MarkMakies/Roverling/Roverling102.kicad_sch

## KiCad design Roverling102.kicad_sch (2023-07-21)

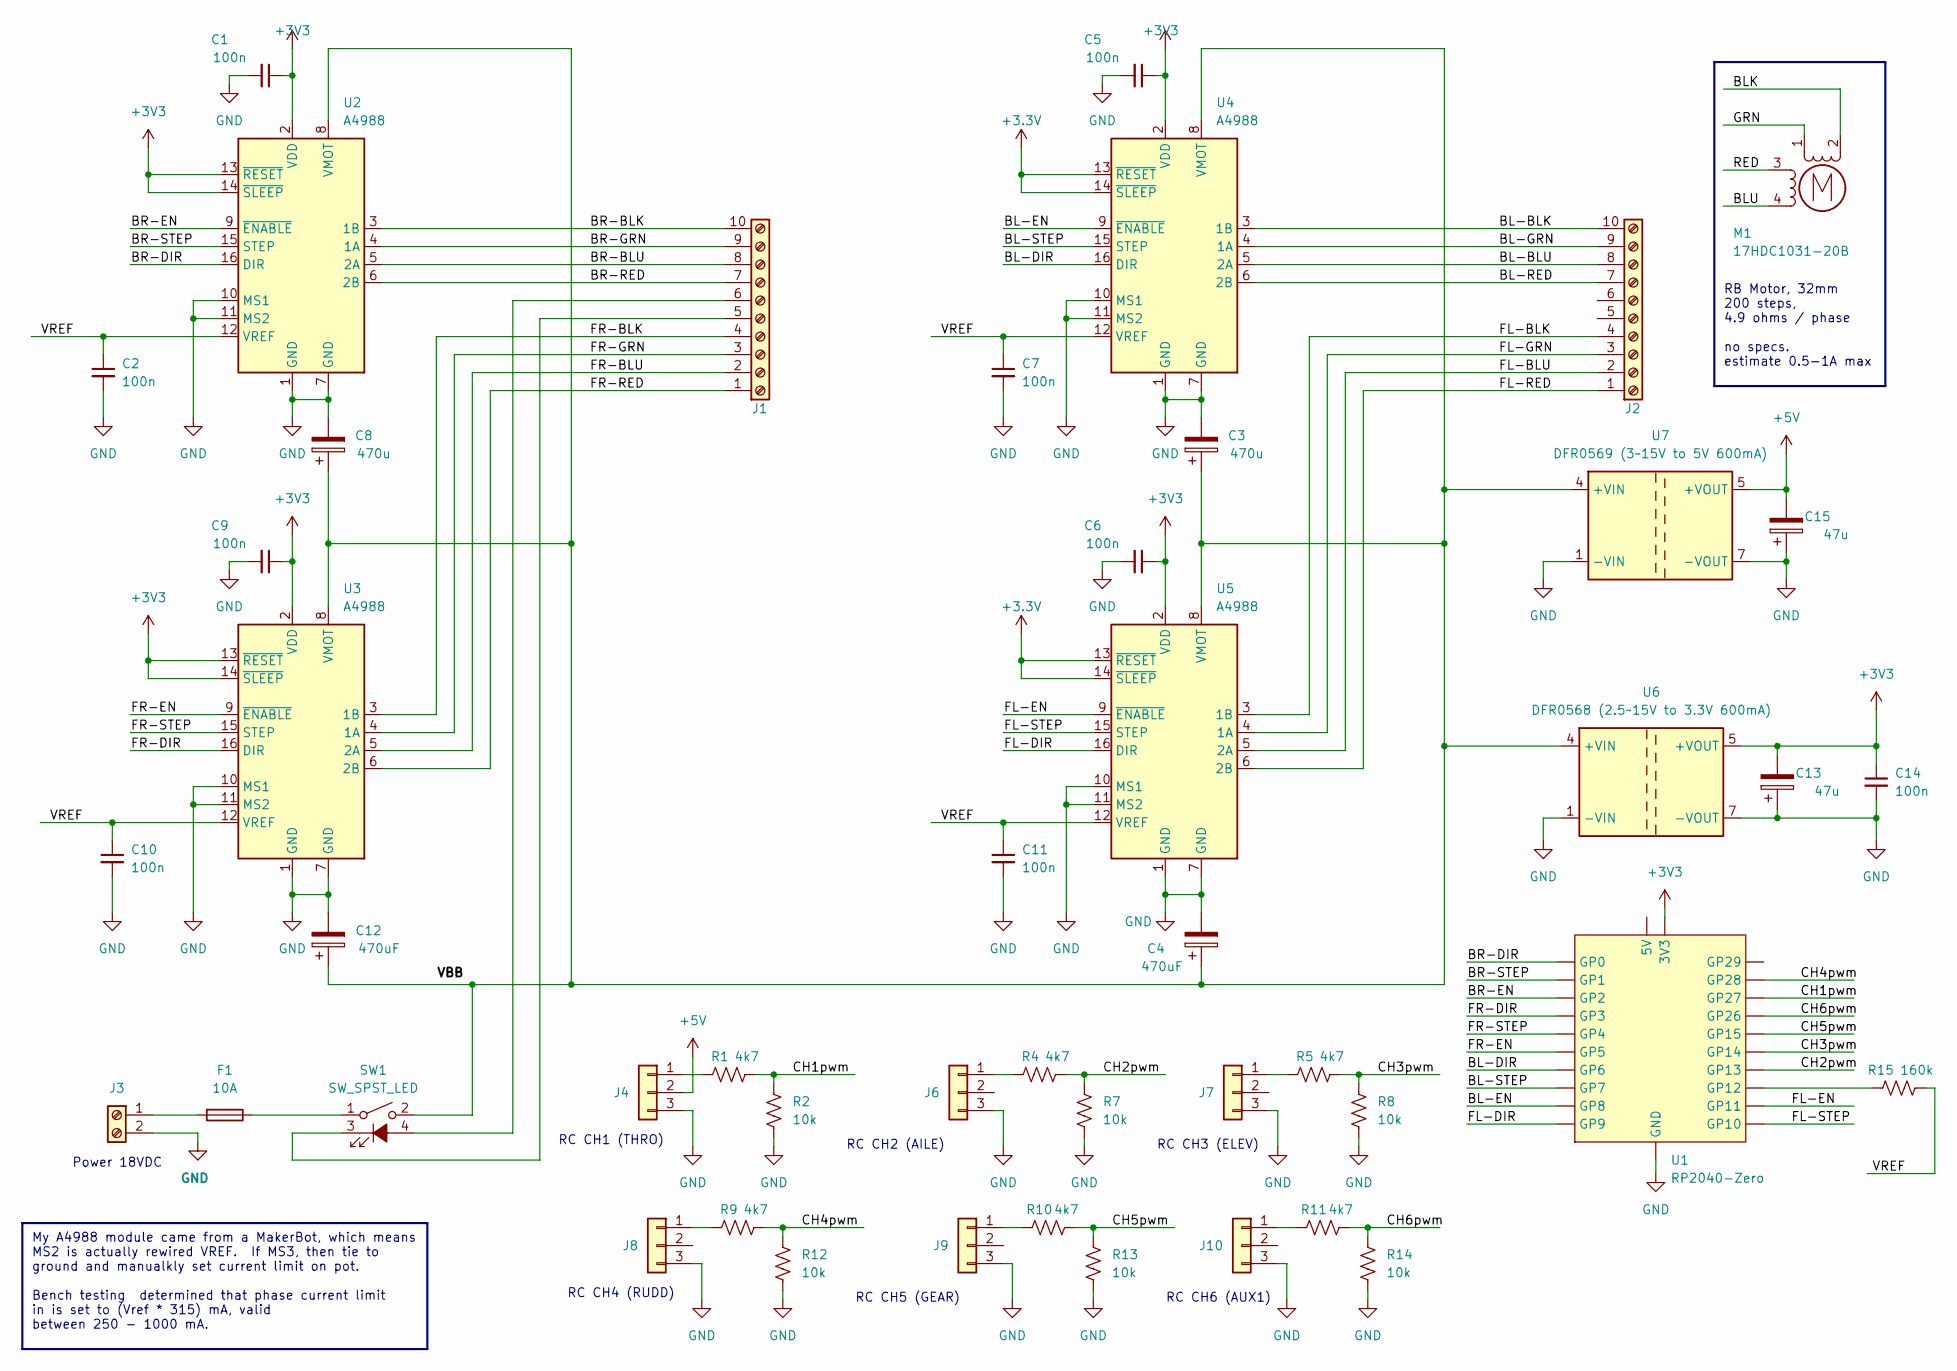
[picture p10: schematic Roverling102.kicad_sch]

Parts:
C1, C2, C5, C6, C7, C9, C10, C11, C14: 100n
C3, C8: 470u
C4, C12: 470uF
C13, C15: 47u
F1: 10A
J1, J2: Screw_Terminal
J3: Screw_Terminal_01x02
J4, J6, J7, J8, J9, J10: Conn_01x03
M1: 17HDC1031-20B
R1, R4, R5, R9, R10, R11: 4k7
R2, R7, R8, R12, R13, R14: 10k
R15: 160k
SW1: SW_SPST_LED
U1: RP2040-Zero
U2, U3, U4, U5: A4988; Pololu_Breakout-16_15.2x20.3mm
U6: DFR0568 (2.5~15V to 3.3V 600mA); Converter_DCDC_Murata_CRE1xxxxxxDC_THT
U7: DFR0569 (3~15V to 5V 600mA); Converter_DCDC_Murata_CRE1xxxxxxDC_THT

Connections:
+3.3V: U4.13 (~RESET), U4.14 (~SLEEP), U5.13 (~RESET), U5.14 (~SLEEP)
+3V3: C1.1, C5.1, C6.1, C9.1, C13.2, C14.1, U1.21 (3V3), U2.2 (VDD), U2.13 (~RESET), U2.14 (~SLEEP), U3.2 (VDD), U3.13 (~RESET), U3.14 (~SLEEP), U4.2 (VDD), U5.2 (VDD), U6.5 (+VOUT)
+5V: C15.2, J4.2, U7.5 (+VOUT)
BL-BLK: J2.10, U4.3 (1B)
BL-BLU: J2.8, U4.5 (2A)
BL-DIR: U1.7 (GP6), U4.16 (DIR)
BL-EN: U1.9 (GP8), U4.9 (~ENABLE)
BL-GRN: J2.9, U4.4 (1A)
BL-RED: J2.7, U4.6 (2B)
BL-STEP: U1.8 (GP7), U4.15 (STEP)
BLK: M1.2 (-)
BLU: M1.4
BR-BLK: J1.10, U2.3 (1B)
BR-BLU: J1.8, U2.5 (2A)
BR-DIR: U1.1 (GP0), U2.16 (DIR)
BR-EN: U1.3 (GP2), U2.9 (~ENABLE)
BR-GRN: J1.9, U2.4 (1A)
BR-RED: J1.7, U2.6 (2B)
BR-STEP: U1.2 (GP1), U2.15 (STEP)
CH1pwm: R1.1, R2.2, U1.18 (GP27)
CH2pwm: R4.1, R7.2, U1.14 (GP13)
CH3pwm: R5.1, R8.2, U1.15 (GP14)
CH4pwm: R9.1, R12.2, U1.19 (GP28)
CH5pwm: R10.1, R13.2, U1.16 (GP15)
CH6pwm: R11.1, R14.2, U1.17 (GP26)
FL-BLK: J2.4, U5.3 (1B)
FL-BLU: J2.2, U5.5 (2A)
FL-DIR: U1.10 (GP9), U5.16 (DIR)
FL-EN: U1.12 (GP11), U5.9 (~ENABLE)
FL-GRN: J2.3, U5.4 (1A)
FL-RED: J2.1, U5.6 (2B)
FL-STEP: U1.11 (GP10), U5.15 (STEP)
FR-BLK: J1.4, U3.3 (1B)
FR-BLU: J1.2, U3.5 (2A)
FR-DIR: U1.4 (GP3), U3.16 (DIR)
FR-EN: U1.6 (GP5), U3.9 (~ENABLE)
FR-GRN: J1.3, U3.4 (1A)
FR-RED: J1.1, U3.6 (2B)
FR-STEP: U1.5 (GP4), U3.15 (STEP)
GND: C1.2, C2.2, C3.2, C4.2, C5.2, C6.2, C7.2, C8.2, C9.2, C10.2, C11.2, C12.2, C13.1, C14.2, C15.1, J3.2, J4.3, J6.3, J7.3, J8.3, J9.3, J10.3, R2.1, R7.1, R8.1, R12.1, R13.1, R14.1, U1.23 (GND), U2.1 (GND), U2.7 (GND), U2.10 (MS1), U2.11 (MS2), U3.1 (GND), U3.7 (GND), U3.10 (MS1), U3.11 (MS2), U4.1 (GND), U4.7 (GND), U4.10 (MS1), U4.11 (MS2), U5.1 (GND), U5.7 (GND), U5.10 (MS1), U5.11 (MS2), U6.1 (-VIN), U6.7 (-VOUT), U7.1 (-VIN), U7.7 (-VOUT)
GRN: M1.1
unnamed: C3.1, C4.1, C8.1, C12.1, SW1.2, U2.8 (VMOT), U3.8 (VMOT), U4.8 (VMOT), U5.8 (VMOT), U6.4 (+VIN), U7.4 (+VIN)
unnamed: F1.1, SW1.1
unnamed: F1.2, J3.1
unnamed: J1.5, SW1.3 (K)
unnamed: J1.6, SW1.4 (A)
unnamed: J4.1, R1.2
unnamed: J6.1, R4.2
unnamed: J7.1, R5.2
unnamed: J8.1, R9.2
unnamed: J9.1, R10.2
unnamed: J10.1, R11.2
unnamed: R15.2, U1.13 (GP12)
RED: M1.3
VREF: C2.1, C7.1, C10.1, C11.1, R15.1, U2.12 (VREF), U3.12 (VREF), U4.12 (VREF), U5.12 (VREF)

Notes on the sheet:
RC CH4 (RUDD)
My A4988 module came from a MakerBot, which means MS2 is actually rewired VREF. If MS3, then tie to ground and manualkly set current limit on pot. Bench testing determined that phase current limit in is set to (Vref * 315) mA, valid between 250 - 1000 mA.
RC CH6 (AUX1)
RC CH2 (AILE)
RC CH1 (THRO)
RC CH3 (ELEV)
RB Motor, 32mm 200 steps, 4.9 ohms / phase no specs. estimate 0.5-1A max
Power 18VDC
RC CH5 (GEAR)
